Kadnat/DLproject/electronic diagrams/wire_soluce.drawio.png

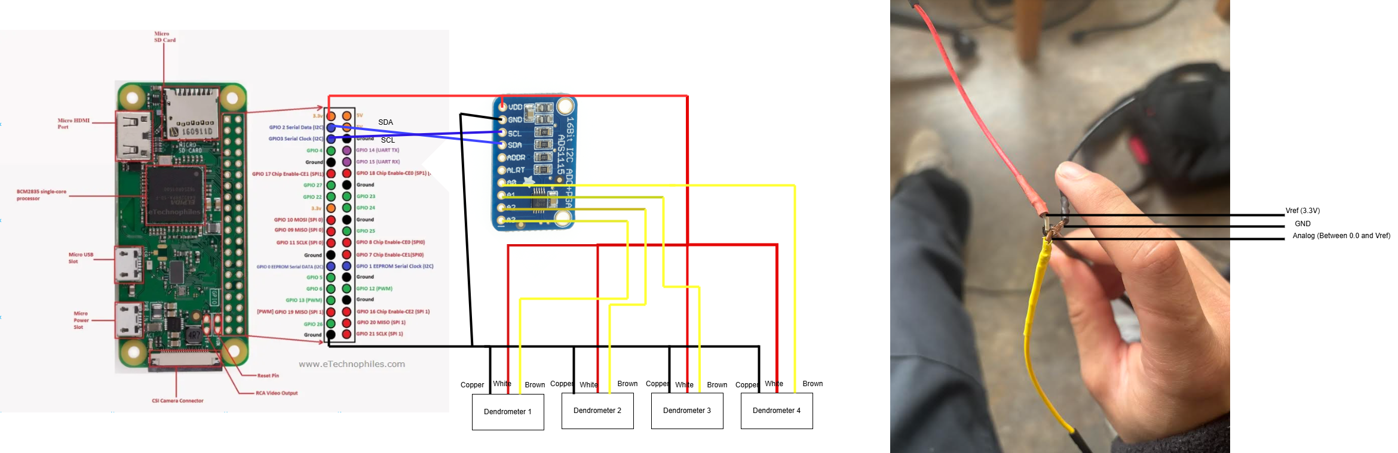
electronic diagrams/wire_soluce.drawio.png
