Kadnat/DLproject/firmware boards/adafruit-circuitpython-bundle-8.x-mpy-20240625/examples/pycamera/filter/testpattern_208x208.jpg

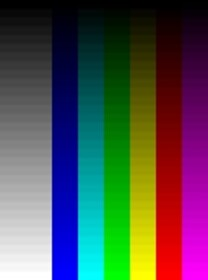
firmware boards/adafruit-circuitpython-bundle-8.x-mpy-20240625/examples/pycamera/filter/testpattern_208x208.jpg
