Kadnat/DLproject/firmware boards/adafruit-circuitpython-bundle-8.x-mpy-20240625/examples/74hc595/74hc595_daisy_chain/figs/ItsyBitsyM0_w_LEDs_and_two_shift_registers.gif

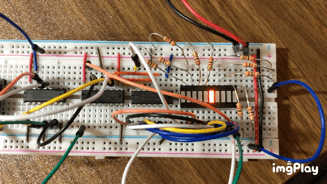
firmware boards/adafruit-circuitpython-bundle-8.x-mpy-20240625/examples/74hc595/74hc595_daisy_chain/figs/ItsyBitsyM0_w_LEDs_and_two_shift_registers.gif
