Kadnat/DLproject/firmware boards/adafruit-circuitpython-bundle-8.x-mpy-20240625/examples/acep7in/display_ruler_720p.bmp

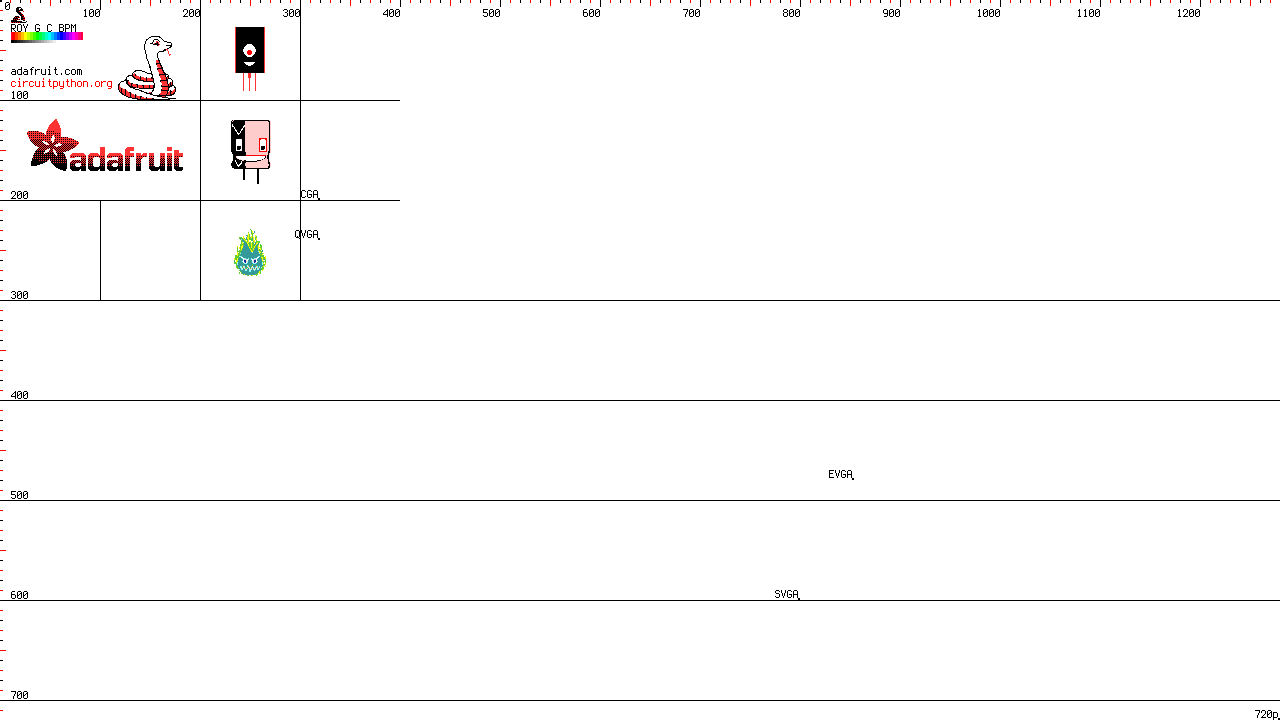
firmware boards/adafruit-circuitpython-bundle-8.x-mpy-20240625/examples/acep7in/display_ruler_720p.bmp
