Kadnat/DLproject/firmware boards/adafruit-circuitpython-bundle-8.x-mpy-20240625/examples/clue/clue_slideshow/adafruit_products_Blinka_240x240.bmp

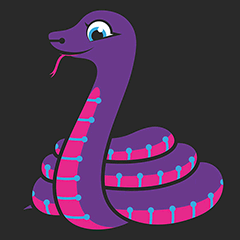
firmware boards/adafruit-circuitpython-bundle-8.x-mpy-20240625/examples/clue/clue_slideshow/adafruit_products_Blinka_240x240.bmp
