Kadnat/DLproject/firmware boards/adafruit-circuitpython-bundle-8.x-mpy-20240625/examples/displayio_flipclock/bottom_animation_sheet_small_5frames.bmp

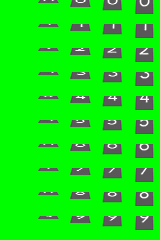
firmware boards/adafruit-circuitpython-bundle-8.x-mpy-20240625/examples/displayio_flipclock/bottom_animation_sheet_small_5frames.bmp
