Kadnat/DLproject/firmware boards/adafruit-circuitpython-bundle-8.x-mpy-20240625/examples/displayio_flipclock/grey_top_animation_sheet.bmp

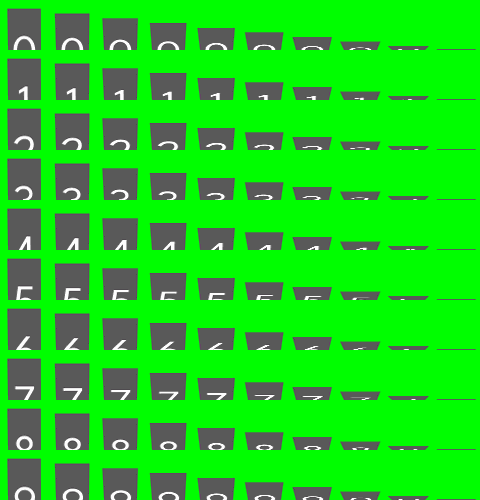
firmware boards/adafruit-circuitpython-bundle-8.x-mpy-20240625/examples/displayio_flipclock/grey_top_animation_sheet.bmp
