Kadnat/DLproject/firmware boards/adafruit-circuitpython-bundle-8.x-mpy-20240625/examples/displayio_flipclock/parchment_bottom_animation_sheet.bmp

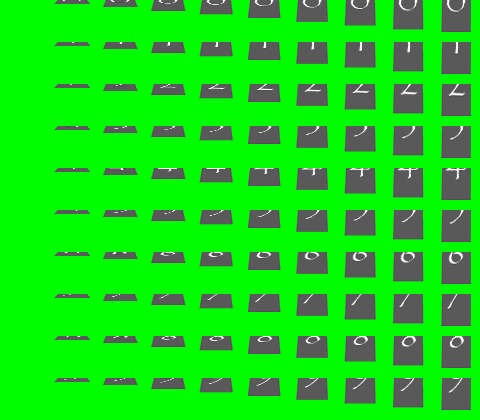
firmware boards/adafruit-circuitpython-bundle-8.x-mpy-20240625/examples/displayio_flipclock/parchment_bottom_animation_sheet.bmp
