Kadnat/DLproject/firmware boards/adafruit-circuitpython-bundle-8.x-mpy-20240625/examples/displayio_layout/hotplug_sensor_examples/images/BGimage4.bmp

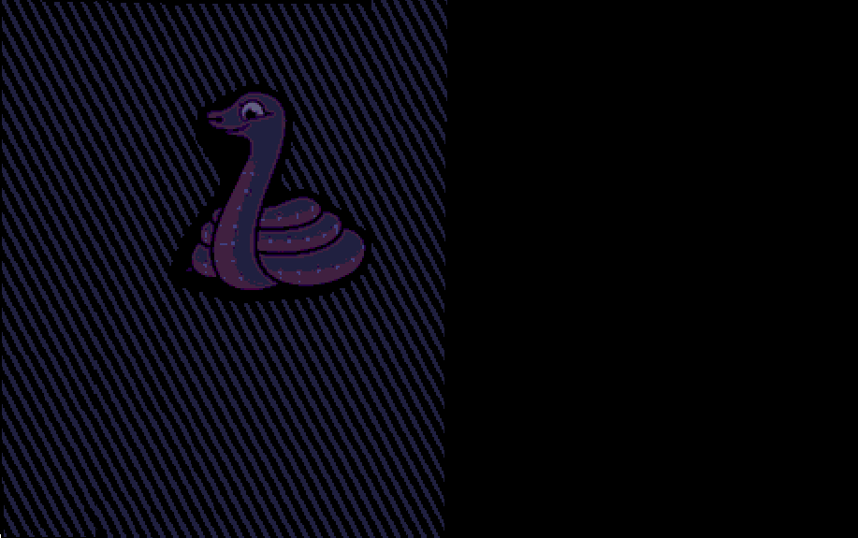
firmware boards/adafruit-circuitpython-bundle-8.x-mpy-20240625/examples/displayio_layout/hotplug_sensor_examples/images/BGimage4.bmp
