Kadnat/DLproject/firmware boards/adafruit-circuitpython-bundle-8.x-mpy-20240625/examples/ek79686/display_ruler.bmp

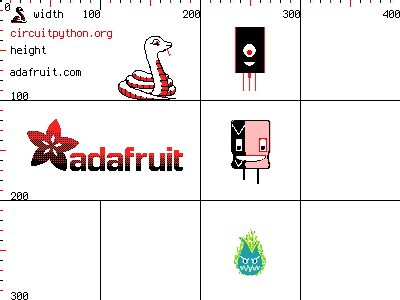
firmware boards/adafruit-circuitpython-bundle-8.x-mpy-20240625/examples/ek79686/display_ruler.bmp
