Kadnat/DLproject/firmware boards/adafruit-circuitpython-bundle-8.x-mpy-20240625/examples/epd/epd_bonnet_blinka_250x122.bmp

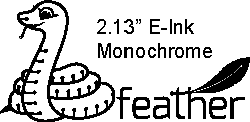
firmware boards/adafruit-circuitpython-bundle-8.x-mpy-20240625/examples/epd/epd_bonnet_blinka_250x122.bmp
