Kadnat/DLproject/firmware boards/adafruit-circuitpython-bundle-8.x-mpy-20240625/examples/gizmo/thermometer_background.bmp

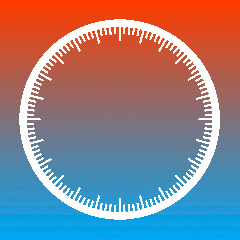
firmware boards/adafruit-circuitpython-bundle-8.x-mpy-20240625/examples/gizmo/thermometer_background.bmp
