Kadnat/DLproject/firmware boards/adafruit-circuitpython-bundle-8.x-mpy-20240625/examples/imageload/images/color_wheel.bmp

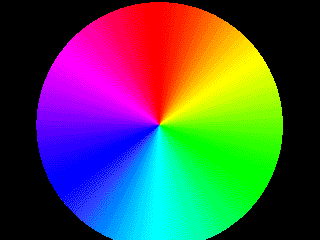
firmware boards/adafruit-circuitpython-bundle-8.x-mpy-20240625/examples/imageload/images/color_wheel.bmp
