Kadnat/DLproject/firmware boards/adafruit-circuitpython-bundle-8.x-mpy-20240625/examples/monsterm4sk/small_triangle_eye.bmp

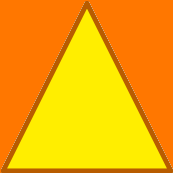
firmware boards/adafruit-circuitpython-bundle-8.x-mpy-20240625/examples/monsterm4sk/small_triangle_eye.bmp
