Kadnat/DLproject/firmware boards/adafruit-circuitpython-bundle-8.x-mpy-20240625/examples/pycamera/overlay/blinka_emoji_rgb888.bmp

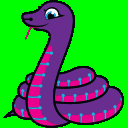
firmware boards/adafruit-circuitpython-bundle-8.x-mpy-20240625/examples/pycamera/overlay/blinka_emoji_rgb888.bmp
