Kadnat/DLproject/firmware boards/adafruit-circuitpython-bundle-8.x-mpy-20240625/examples/pycamera/overlay/heart_frame_rgb888.bmp

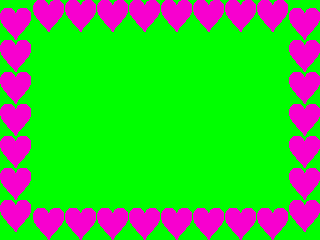
firmware boards/adafruit-circuitpython-bundle-8.x-mpy-20240625/examples/pycamera/overlay/heart_frame_rgb888.bmp
