Kadnat/DLproject/firmware boards/adafruit-circuitpython-bundle-8.x-mpy-20240625/examples/pyoa/cave/page01.bmp

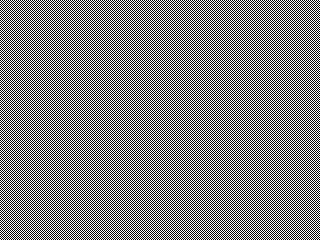
firmware boards/adafruit-circuitpython-bundle-8.x-mpy-20240625/examples/pyoa/cave/page01.bmp
