Kadnat/DLproject/firmware boards/adafruit-circuitpython-bundle-8.x-mpy-20240625/examples/pyoa/cyoa/home.bmp

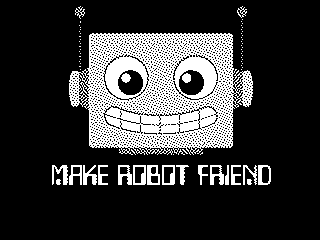
firmware boards/adafruit-circuitpython-bundle-8.x-mpy-20240625/examples/pyoa/cyoa/home.bmp
