Kadnat/DLproject/firmware boards/adafruit-circuitpython-bundle-8.x-mpy-20240625/examples/pyoa/cyoa/startup.bmp

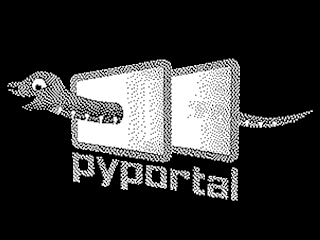
firmware boards/adafruit-circuitpython-bundle-8.x-mpy-20240625/examples/pyoa/cyoa/startup.bmp
