Kadnat/DLproject/firmware boards/adafruit-circuitpython-bundle-8.x-mpy-20240625/examples/ra8875/ra8875_blinka.bmp

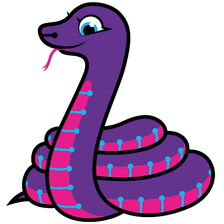
firmware boards/adafruit-circuitpython-bundle-8.x-mpy-20240625/examples/ra8875/ra8875_blinka.bmp
