Kadnat/DLproject/firmware boards/adafruit-circuitpython-bundle-8.x-mpy-20240625/examples/slideshow/images/blue_rectangle.bmp

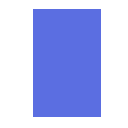
firmware boards/adafruit-circuitpython-bundle-8.x-mpy-20240625/examples/slideshow/images/blue_rectangle.bmp
