Kadnat/DLproject/firmware boards/adafruit-circuitpython-bundle-8.x-mpy-20240625/examples/slideshow/images/purple_oval.bmp

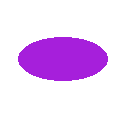
firmware boards/adafruit-circuitpython-bundle-8.x-mpy-20240625/examples/slideshow/images/purple_oval.bmp
