Kadnat/DLproject/firmware boards/adafruit-circuitpython-bundle-8.x-mpy-20240625/examples/wii_classic/wii_classic.bmp

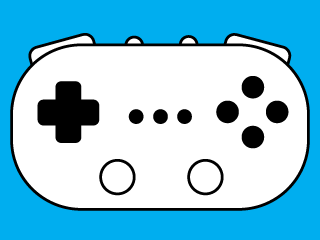
firmware boards/adafruit-circuitpython-bundle-8.x-mpy-20240625/examples/wii_classic/wii_classic.bmp
