Kadnat/DLproject/electronic diagrams/schematics_node_measure.drawio.png

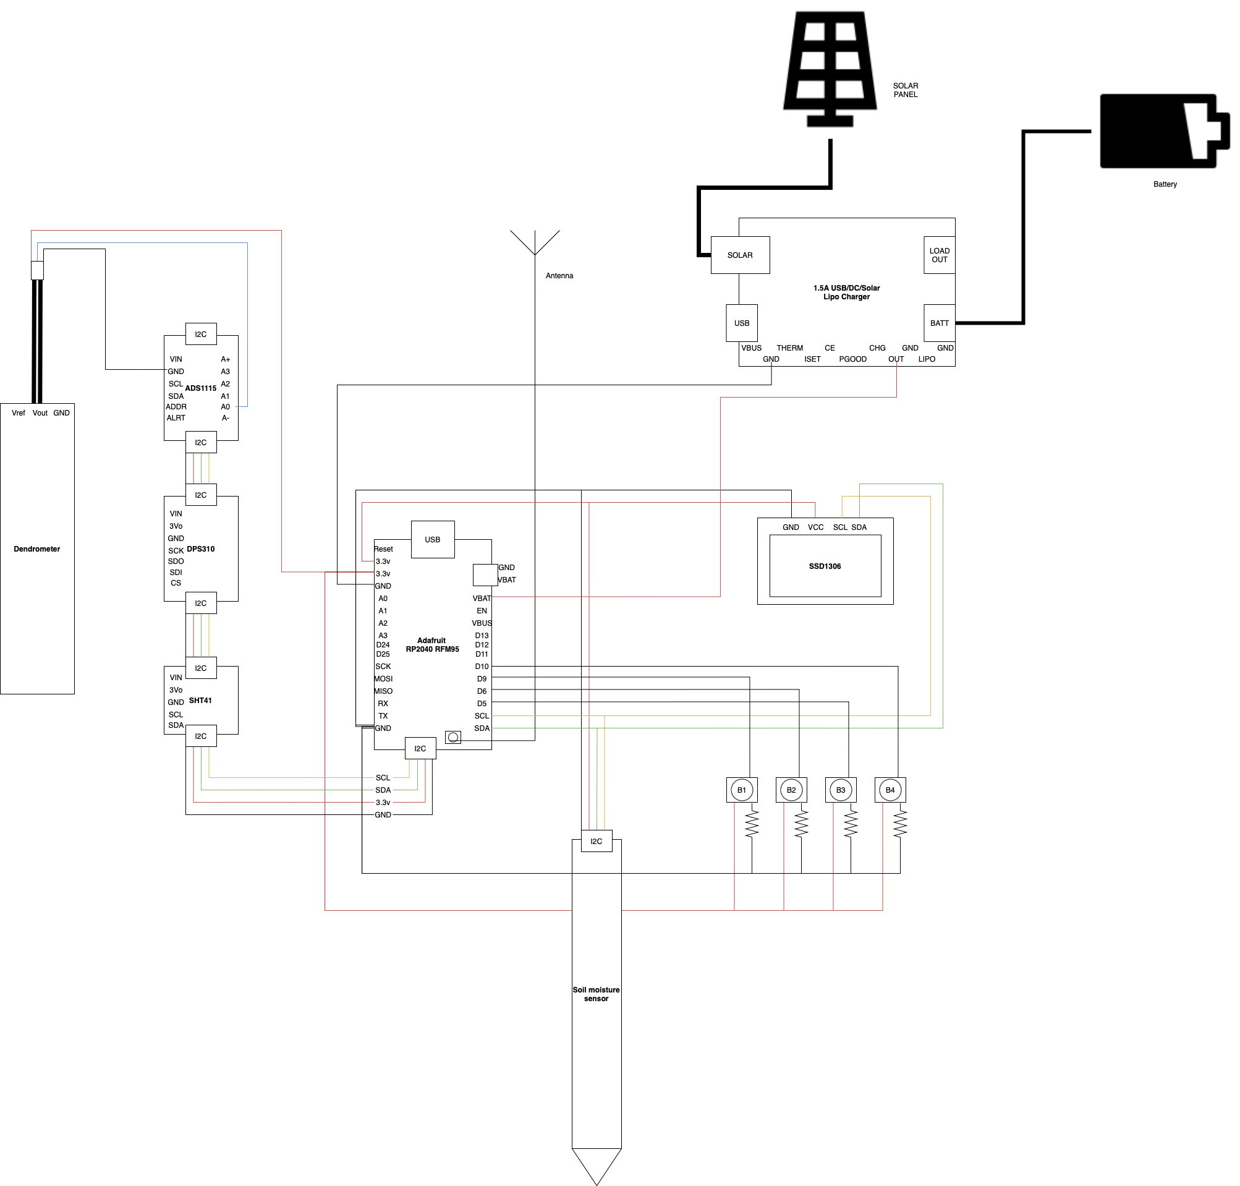
electronic diagrams/schematics_node_measure.drawio.png
