Kadnat/DLproject/firmware boards/adafruit-circuitpython-bundle-8.x-mpy-20240625/examples/imageload/images/test_image.png

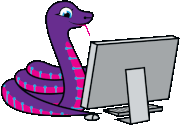
firmware boards/adafruit-circuitpython-bundle-8.x-mpy-20240625/examples/imageload/images/test_image.png
